knobunc/glowtape/firmware/bitmap-contents.h

#ifndef BITMAP_CONTENTS_H
#define BITMAP_CONTENTS_H

#include <cstdint>
#include <cstdlib>

// Make writing bitmaps a bit more readable.
constexpr uint64_t operator""_bitmap(const char *str, size_t) {
  uint64_t result = 0;
  for (/**/; *str; ++str) {
    result |= (*str != ' ');
    result <<= static_cast<uint64_t>(1);
  }
  return result;
}

constexpr uint64_t kJollyWrencherBitmap[] = {
    "                                                                "_bitmap,
    "       #####                                      #####         "_bitmap,
    "        ######                                  ######          "_bitmap,
    "         ######                                ######           "_bitmap,
    "           ####                                ####             "_bitmap,
    "           #####                              #####             "_bitmap,
    "          ######                              ######            "_bitmap,
    " #        ######                              ######        #   "_bitmap,
    " ##      #######                              #######      ##   "_bitmap,
    " ###    ########                              ########    ###   "_bitmap,
    " ####  ##########                            ##########  ####   "_bitmap,
    "  #################                        #################    "_bitmap,
    "  ##################                      ##################    "_bitmap,
    "   ##################       ######       ##################     "_bitmap,
    "    ##################   ############   ##################      "_bitmap,
    "      ###############  ################  ###############        "_bitmap,
    "            ########  ##################  ########              "_bitmap,
    "             ######  #################### #######               "_bitmap,
    "              ##### ###################### #####                "_bitmap,
    "               ###  ######################  ###                 "_bitmap,
    "                 # ######################## ##                  "_bitmap,
    "                  ##########################                    "_bitmap,
    "                  ##########################                    "_bitmap,
    "                  ##########################                    "_bitmap,
    "                 ############################                   "_bitmap,
    "                 ######    ########    ######                   "_bitmap,
    "                 #####      ######      #####                   "_bitmap,
    "                 ####        ####        ####                   "_bitmap,
    "                 ####       ######       ####                   "_bitmap,
    "                 ####      ########      ####                   "_bitmap,
    "                 ####    ############    ####                   "_bitmap,
    "                 ####   ##############   ####                   "_bitmap,
    "                 ##### ################ #####                   "_bitmap,
    "                 ############## #############                   "_bitmap,
    "                  ############  ############                    "_bitmap,
    "                  ############  ############                    "_bitmap,
    "               ##  ###########  ###########  ##                 "_bitmap,
    "              #### ######################## ####                "_bitmap,
    "             #####  ######################  #####               "_bitmap,
    "            #######  ####################  #######              "_bitmap,
    "      ############## #################### ##############        "_bitmap,
    "    #################  ################  #################      "_bitmap,
    "   ##################  ################  ##################     "_bitmap,
    "  ##################   ################   ##################    "_bitmap,
    "  ################     ##### #### #####     ################    "_bitmap,
    " ####  ##########       ###   ##   ###       ##########  ####   "_bitmap,
    " ###    ########                              ########    ###   "_bitmap,
    " ##      #######                              #######      ##   "_bitmap,
    " #        ######                              ######        #   "_bitmap,
    "           #####                              #####             "_bitmap,
    "           #####                              #####             "_bitmap,
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
    "##############    ##    ######  ##  ##  ####    ##       "_bitmap,
    "##          ##  ##  ######  ######      ##               "_bitmap,
    "##          ##  ##  ######  ######      ##               "_bitmap,
    "##  ######  ##      ##    ##################    ##       "_bitmap,
    "##  ######  ##      ##    ##################    ##       "_bitmap,
    "##  ######  ##    ##      ######  ##    ########         "_bitmap,
    "##  ######  ##    ##      ######  ##    ########         "_bitmap,
    "##  ######  ##  ##  ####        ##      ##    ####       "_bitmap,
    "##  ######  ##  ##  ####        ##      ##    ####       "_bitmap,
    "##          ##  ######    ##    ##  ######               "_bitmap,
    "##          ##  ######    ##    ##  ######               "_bitmap,
    "##############  ############    ######    ##    ##       "_bitmap,
    "##############  ############    ######    ##    ##       "_bitmap,
};

#endif
