knobunc/glowtape/firmware/frame-printer.h

#ifndef FRAME_PRINTER_H
#define FRAME_PRINTER_H

#include <algorithm>
#include <cstdint>

#include "hardware/gpio.h"
#include "hardware/spi.h"
#include "pico/time.h"

enum class ScreenAspect {
  kAlongWidth,   // X axis along width; (0, 0) at top left after full pull.
  kAlongLength,  // X axis along length; (0, 0) first in pull, at top.
};

// Sequence
//  StartNewImage();
//  SetPixel()...
//  for (SendStart(); SendNext(); /**/) {
//    WaitForSync();
//    LighFlash(flashmillis);
//  }
//
class FramePrinter {
  static constexpr int kMaxRows = 1024;
  static constexpr uint8_t kLightFlashPin = 8;
  static constexpr uint8_t kEvenOddLineOffset = 4;

 public:
  using RowBits_t = uint64_t;
  FramePrinter(int spiTxPin, spi_inst_t *instance) : instance_(instance) {
    spi_init(instance_, 1'000'000);
    spi_set_format(instance_, 8,            // Regylar 8 bits transfer
                   spi_cpol_t::SPI_CPOL_1,  // pos polarity
                   spi_cpha_t::SPI_CPHA_1,  // phase
                   spi_order_t::SPI_MSB_FIRST);
    // Luckily, the RP2040 has pin-muxing pretty standardized and we can derive
    // the remaining pins from just knowing one pin.
    const int spiSckPin = spiTxPin - 1;
    const int spiCsPin = spiTxPin - 2;  // Also called 'latch' on glowxels
    gpio_set_function(spiTxPin, GPIO_FUNC_SPI);
    gpio_set_function(spiSckPin, GPIO_FUNC_SPI);
    gpio_set_function(spiCsPin, GPIO_FUNC_SPI);

    gpio_init(kLightFlashPin);
    gpio_set_dir(kLightFlashPin, GPIO_OUT);
    gpio_put(kLightFlashPin, true);  // ~OE
  }

  // Start sending the new
  void SendStart() {
    send_pos_ = row_end_ - 1;
    if (send_pos_ >= kMaxRows - kEvenOddLineOffset) return;
    // We want to start the line offset earlier to cover all the bits.
    for (uint8_t i = 0; i < kEvenOddLineOffset; ++i) {
      row_[++send_pos_] = 0;
    }
  }

  // Send next line. Can be done independently of actually flashing the light.
  // Returns 'true' if there is more to send.
  bool SendNext() {
    if (send_pos_ < 0) {
      SendData(0);  // Make sure no stray LEDs go on when OE is pulled down.
      return false;
    }
    SendData(assembleLedDataAt(send_pos_));
    --send_pos_;
    return true;
  }

  void LightFlash(uint16_t milliseconds) {
    gpio_put(kLightFlashPin, false);  // ~OE
    sleep_ms(milliseconds);
    gpio_put(kLightFlashPin, true);
  }

  void StartNewImage(ScreenAspect type) {
    // Clear out previous image.
    for (int i = 0; i < row_end_; ++i) {
      row_[i] = 0;
    }
    aspect_type_ = type;
    row_end_ = 0;
  }

  // Set pixel on (x,y); interpreted in the context of Screenaspect
  void SetPixel(int x, int y, bool on = true) {
    constexpr int kMaxColumns = sizeof(RowBits_t) * 8;
    if (aspect_type_ == ScreenAspect::kAlongLength) {
      std::swap(x, y);
      x = 64 - x;
    }
    if (x < 0 || x >= kMaxColumns) {
      return;
    }

    RowBits_t &to_modify = at(y);
    constexpr RowBits_t kLeftMostBit = static_cast<RowBits_t>(1) << 63;
    if (on) {
      to_modify |= kLeftMostBit >> x;
    } else {
      to_modify &= ~(kLeftMostBit >> x);
    }
  }

  // Provides access to the given row, possibly expanding the current image.
  RowBits_t &at(int r) {
    if (r < 0 || r >= kMaxRows) return row_[kMaxRows - 1];  // error fallback
    row_end_ = (r >= row_end_) ? (r + 1) : row_end_;        // implicit last
    return row_[r];
  }

  void push_back(RowBits_t row_bits) {
    if (row_end_ >= kMaxRows) return;
    row_[row_end_++] = row_bits;
  }

  size_t size() const { return row_end_; }

  void SendData(RowBits_t value) {
    // rp2040 stores things in LE, but we
    RowBits_t big_endian = __builtin_bswap64(value);  // rp2040 is LE
    spi_write_blocking(instance_, (uint8_t *)&big_endian, sizeof(big_endian));
  }

 private:
  // Get column-offset and shift layoyt ready bits.
  RowBits_t assembleLedDataAt(int row) { return MapToPhysical(BitsAtRow(row)); }

  RowBits_t BitsAtRow(int row) {
    // Even/Odd Pixels are interleaved 4 rows apart.
    RowBits_t result = row_[row] & 0x5555'5555'5555'5555;
    if (row >= 4) result |= row_[row - 4] & 0xAAAA'AAAA'AAAA'AAAA;
    return result;
  }

  // Physical mapping of 64 bits, mapped to the particular layout of the
  // bits in the four 16-bit shift register to LEDs they end up at.
  RowBits_t MapToPhysical(RowBits_t data) {
    return (static_cast<RowBits_t>(MapChipBits(data >> 48)) << 48) |
           (static_cast<RowBits_t>(MapChipBits(data >> 32)) << 32) |
           (static_cast<RowBits_t>(MapChipBits(data >> 16)) << 16) |
           (static_cast<RowBits_t>(MapChipBits(data >> 0)) << 0);
  }

  // Map data of one shift register chip to be from interleaved to the
  // corresponding bits on the top and bottom.
  constexpr uint16_t MapChipBits(uint16_t data) const {
    // -- Led mapping of bits in shift-register vs. position.
    constexpr uint8_t newpos[] = {7, 8,  6, 9,  5, 10, 4, 11,
                                  3, 12, 2, 13, 1, 14, 0, 15};
    // There is probably a delightful hackers bit-fiddling that can do this,
    // but here pedestrian.
    uint16_t result = 0;
    for (uint8_t i = 0; i < 16; ++i) {
      if (data & (1 << i)) result |= (1 << newpos[i]);
    }
    return result;
  }

  RowBits_t row_[kMaxRows] = {0};
  int row_end_ = 0;  // like an end() iterator: the row beyond last.
  ScreenAspect aspect_type_ = ScreenAspect::kAlongWidth;

  int send_pos_ = -1;
  spi_inst_t *const instance_;
};
#endif
